John-Keogh/screen-tapper/images/1.0/IMG_0432.jpg

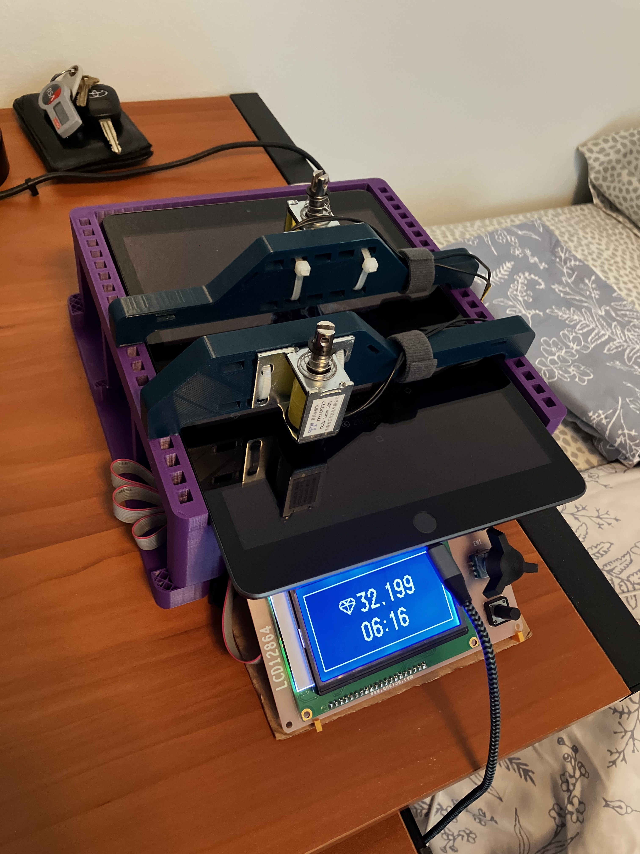
images/1.0/IMG_0432.jpg
