John-Keogh/screen-tapper/images/1.2/IMG_0666.jpg

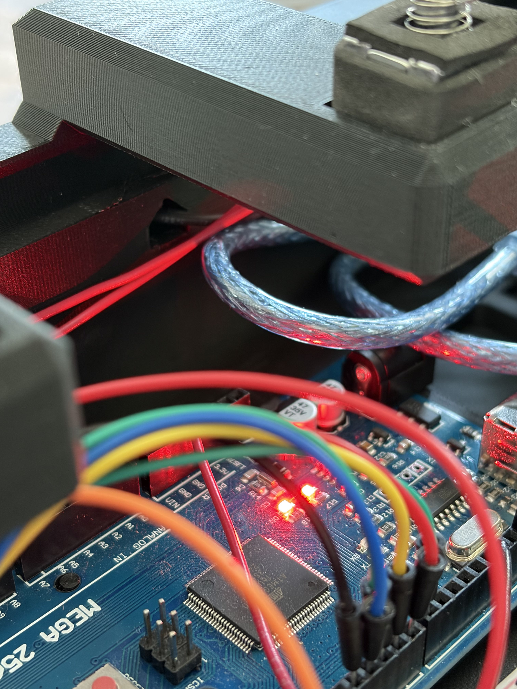
images/1.2/IMG_0666.jpg
