John-Keogh/screen-tapper/hardware/Screen Tapper v1.0.kicad_sch

## KiCad design hardware/Screen Tapper v1.0.kicad_sch (2026-01-04)

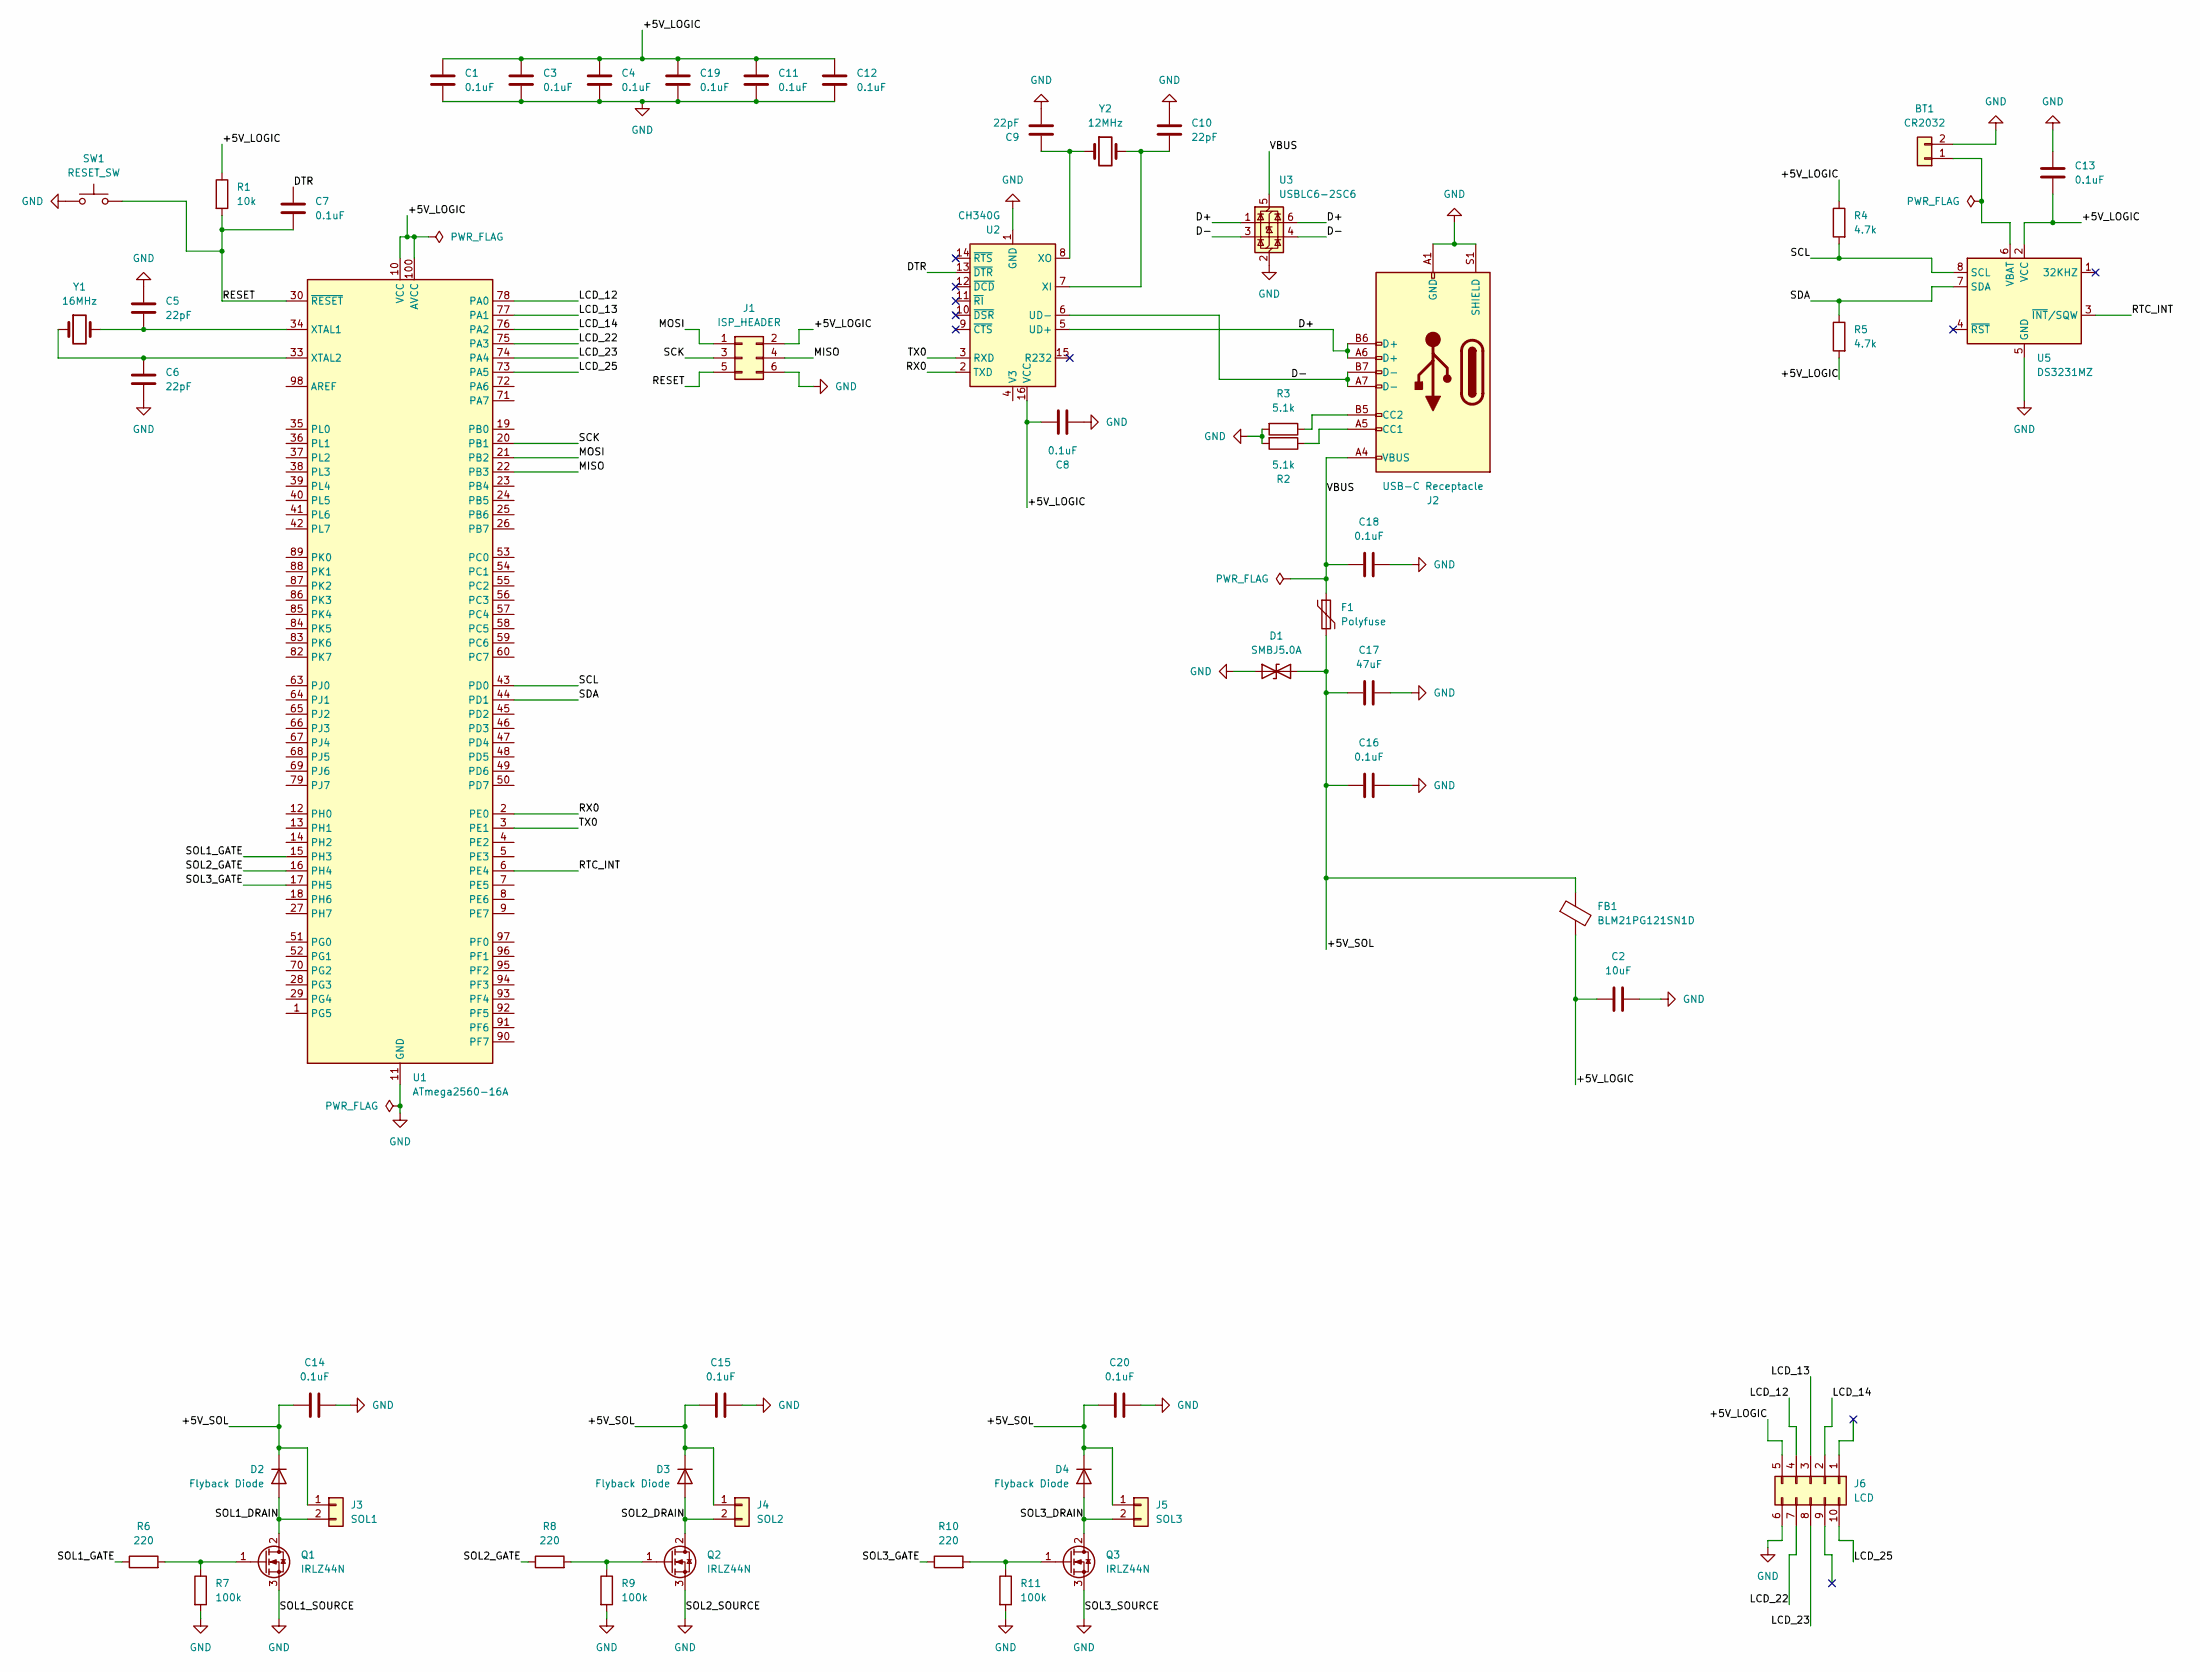
[picture p19: schematic Screen Tapper v1.0.kicad_sch]

Parts:
BT1: CR2032
C1, C3, C4, C7, C8, C11, C12, C13, C14, C15, C16, C18, C19, C20: 0.1uF
C2: 10uF
C5, C6, C9, C10: 22pF
C17: 47uF
D1: SMBJ5.0A
D2, D3, D4: Flyback Diode
F1: Polyfuse
FB1: BLM21PG121SN1D
J1: ISP_HEADER
J2: USB-C Receptacle
J3: SOL1
J4: SOL2
J5: SOL3
J6: LCD
Q1, Q2, Q3: IRLZ44N
R1: 10k
R2, R3: 5.1k
R4, R5: 4.7k
R6, R8, R10: 220
R7, R9, R11: 100k
SW1: RESET_SW
U1: ATmega2560-16A; TQFP-100_14x14mm_P0.5mm
U2: CH340G; SOIC-16_3.9x9.9mm_P1.27mm
U3: USBLC6-2SC6; SOT-23-6
U5: DS3231MZ; SOIC-8_3.9x4.9mm_P1.27mm
Y1: 16MHz
Y2: 12MHz

Connections:
+5V_LOGIC: C1.1, C2.1, C3.1, C4.1, C8.2, C11.1, C12.1, C13.2, C19.1, FB1.2, J1.2, J6.5, R1.1, R4.1, R5.2, U1.10 (VCC), U1.31 (VCC), U1.61 (VCC), U1.80 (VCC), U1.100 (AVCC), U2.16 (VCC), U5.2 (VCC)
+5V_SOL: C14.1, C15.1, C16.1, C17.1, C20.1, D1.2 (A2), D2.1 (K), D3.1 (K), D4.1 (K), F1.2, FB1.1, J3.1, J4.1, J5.1
D+: J2.A6 (D+), J2.B6 (D+), U2.5 (UD+), U3.1 (I/O1), U3.6 (I/O1)
D-: J2.A7 (D-), J2.B7 (D-), U2.6 (UD-), U3.3 (I/O2), U3.4 (I/O2)
DTR: C7.1, U2.13 (~DTR)
GND: BT1.2, C1.2, C2.2, C3.2, C4.2, C5.1, C6.2, C8.1, C9.2, C10.1, C11.2, C12.2, C13.1, C14.2, C15.2, C16.2, C17.2, C18.1, C19.2, C20.2, D1.1 (A1), J1.6, J2.A1 (GND), J2.A12 (GND), J2.B1 (GND), J2.B12 (GND), J2.S1 (SHIELD), J6.6, Q1.3 (S), Q2.3 (S), Q3.3 (S), R2.2, R3.2, R7.2, R9.2, R11.2, SW1.1, U1.11 (GND), U1.32 (GND), U1.62 (GND), U1.81 (GND), U1.99 (GND), U2.1 (GND), U3.2 (GND), U5.5 (GND)
LCD_12: J6.4, U1.78 (PA0)
LCD_13: J6.3, U1.77 (PA1)
LCD_14: J6.2, U1.76 (PA2)
LCD_22: J6.7, U1.75 (PA3)
LCD_23: J6.8, U1.74 (PA4)
LCD_25: J6.10, U1.73 (PA5)
MISO: J1.4, U1.22 (PB3)
MOSI: J1.1, U1.21 (PB2)
unnamed: BT1.1, U5.6 (VBAT)
unnamed: C5.2, U1.34 (XTAL1), Y1.2
unnamed: C6.1, U1.33 (XTAL2), Y1.1
unnamed: C9.1, U2.8 (XO), Y2.1
unnamed: C10.2, U2.7 (XI), Y2.2
unnamed: J2.A5 (CC1), R2.1
unnamed: J2.B5 (CC2), R3.1
unnamed: Q1.1 (G), R6.2, R7.1
unnamed: Q2.1 (G), R8.2, R9.1
unnamed: Q3.1 (G), R10.2, R11.1
RESET: C7.2, J1.5, R1.2, SW1.2, U1.30 (~RESET)
RTC_INT: U1.6 (PE4), U5.3 (~INT/SQW)
RX0: U1.2 (PE0), U2.2 (TXD)
SCK: J1.3, U1.20 (PB1)
SCL: R4.2, U1.43 (PD0), U5.8 (SCL)
SDA: R5.1, U1.44 (PD1), U5.7 (SDA)
SOL1_DRAIN: D2.2 (A), J3.2, Q1.2 (D)
SOL1_GATE: R6.1, U1.15 (PH3)
SOL2_DRAIN: D3.2 (A), J4.2, Q2.2 (D)
SOL2_GATE: R8.1, U1.16 (PH4)
SOL3_DRAIN: D4.2 (A), J5.2, Q3.2 (D)
SOL3_GATE: R10.1, U1.17 (PH5)
TX0: U1.3 (PE1), U2.3 (RXD)
VBUS: C18.2, F1.1, J2.A4 (VBUS), J2.A9 (VBUS), J2.B4 (VBUS), J2.B9 (VBUS), U3.5 (VBUS)
