John-Keogh/screen-tapper/hardware/screen_tapper_pcb.kicad_sch

## KiCad design hardware/screen_tapper_pcb.kicad_sch (2025-07-18)

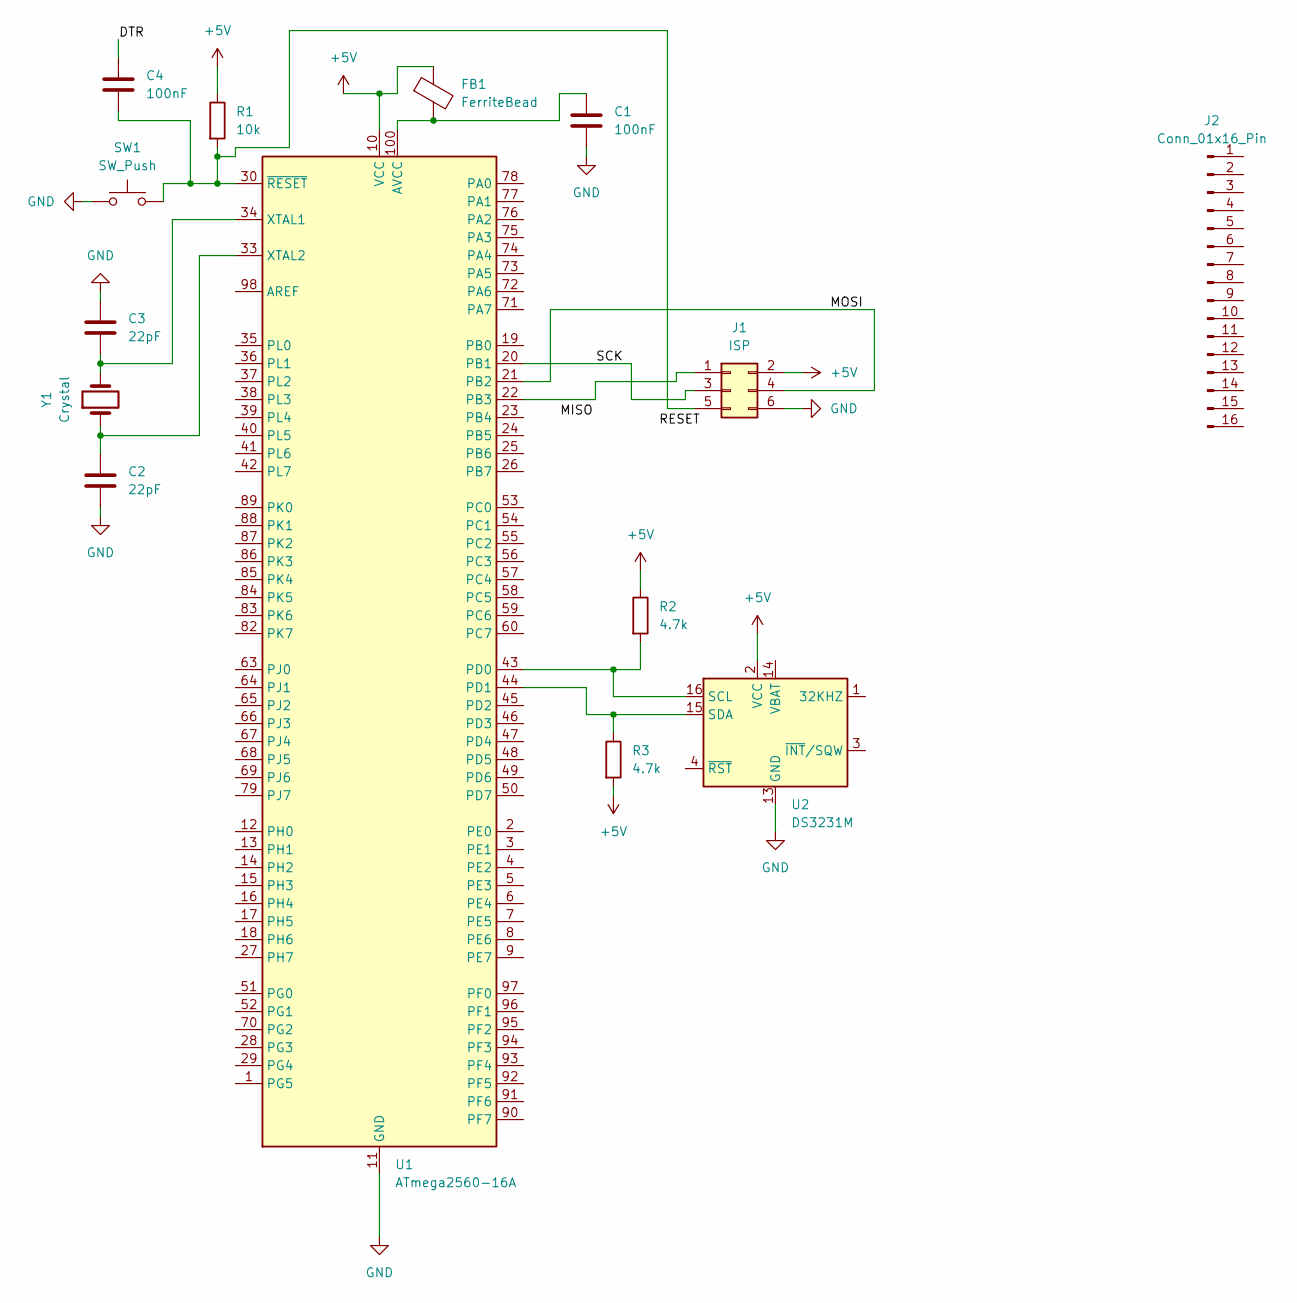
[picture p20: schematic screen_tapper_pcb.kicad_sch]

Parts:
C1, C4: 100nF
C2, C3: 22pF
FB1: FerriteBead
J1: ISP
J2: Conn_01x16_Pin
R1: 10k
R2, R3: 4.7k
SW1: SW_Push
U1: ATmega2560-16A; TQFP-100_14x14mm_P0.5mm
U2: DS3231M; SOIC-16W_7.5x10.3mm_P1.27mm
Y1: Crystal

Connections:
+5V: FB1.1, J1.2, R1.1, R2.1, R3.2, U1.10 (VCC), U1.31 (VCC), U1.61 (VCC), U1.80 (VCC), U2.2 (VCC)
DTR: C4.1
GND: C1.2, C2.2, C3.2, J1.6, SW1.1, U1.11 (GND), U1.32 (GND), U1.62 (GND), U1.81 (GND), U1.99 (GND), U2.5 (GND), U2.6 (GND), U2.7 (GND), U2.8 (GND), U2.9 (GND), U2.10 (GND), U2.11 (GND), U2.12 (GND), U2.13 (GND)
MOSI: J1.4, U1.21 (PB2)
unnamed: C1.1, FB1.2, U1.100 (AVCC)
unnamed: C2.1, U1.33 (XTAL2), Y1.1
unnamed: C3.1, U1.34 (XTAL1), Y1.2
unnamed: C4.2, J1.5, R1.2, SW1.2, U1.30 (~RESET)
unnamed: J1.1, U1.22 (PB3)
unnamed: R2.2, U1.43 (PD0), U2.16 (SCL)
unnamed: R3.1, U1.44 (PD1), U2.15 (SDA)
SCK: J1.3, U1.20 (PB1)
