John-Keogh/screen-tapper/images/1.2/IMG_0661.jpg

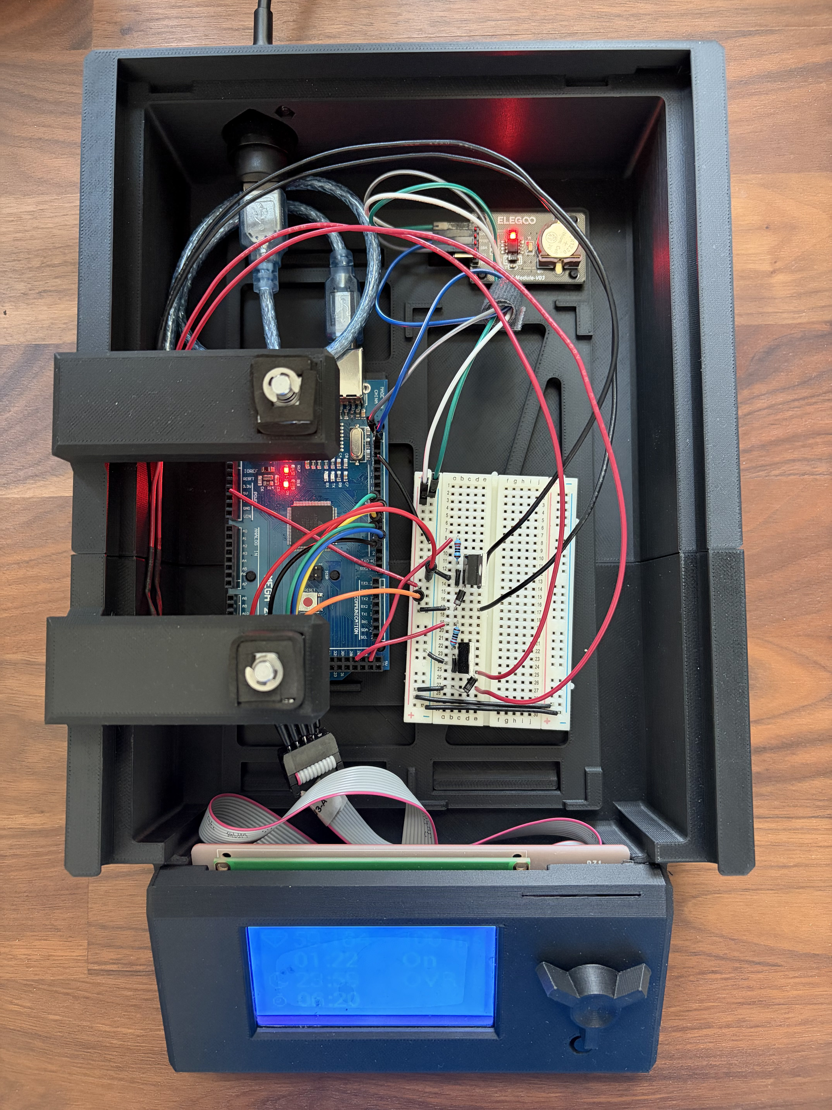
images/1.2/IMG_0661.jpg
