John-Keogh/screen-tapper/images/1.2/IMG_0663.jpg

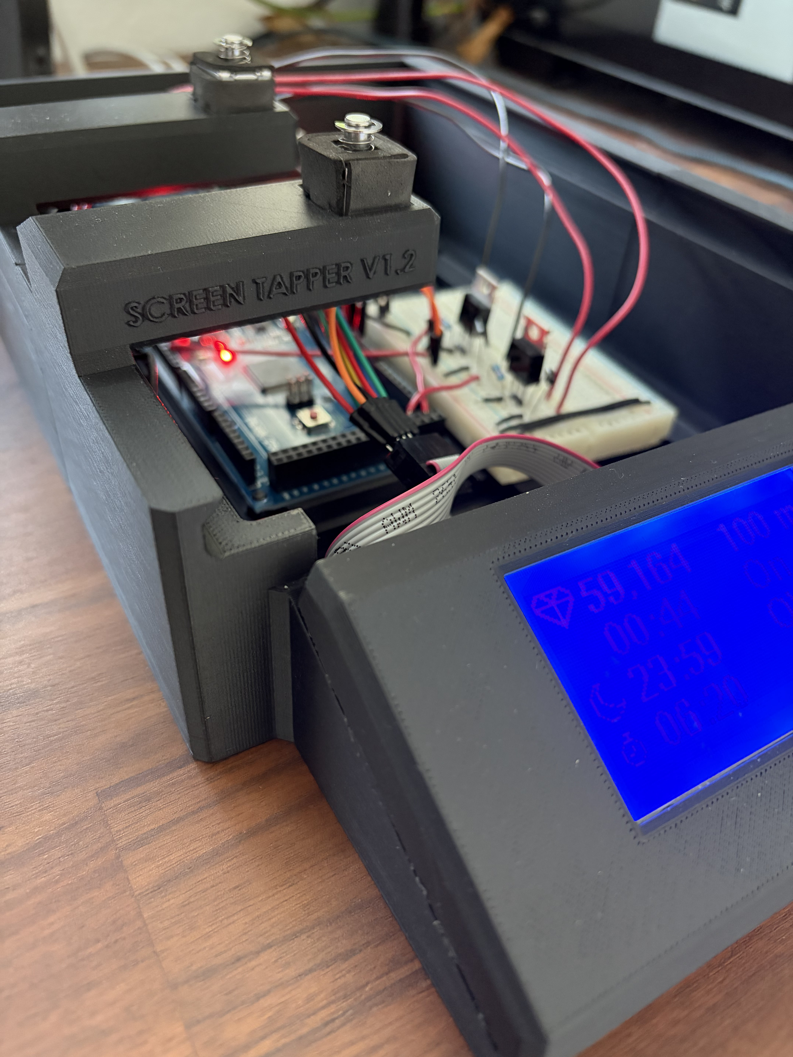
images/1.2/IMG_0663.jpg
