John-Keogh/screen-tapper/images/1.2/IMG_0669.jpg

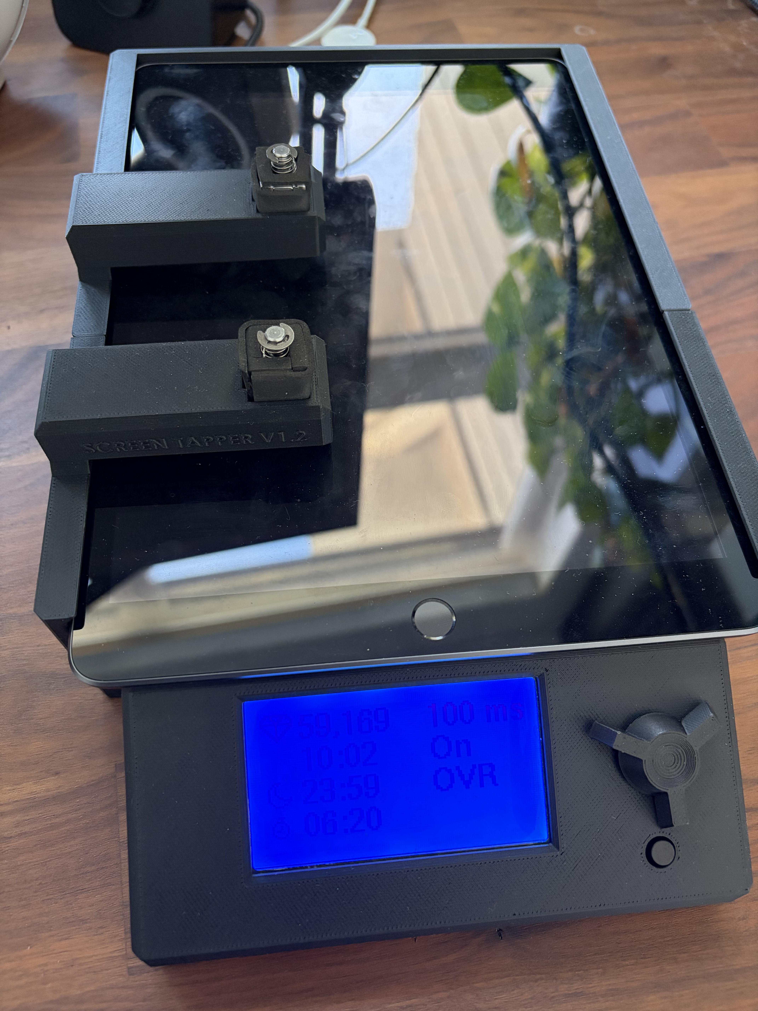
images/1.2/IMG_0669.jpg
