John-Keogh/screen-tapper/images/beta/IMG_9932.jpeg

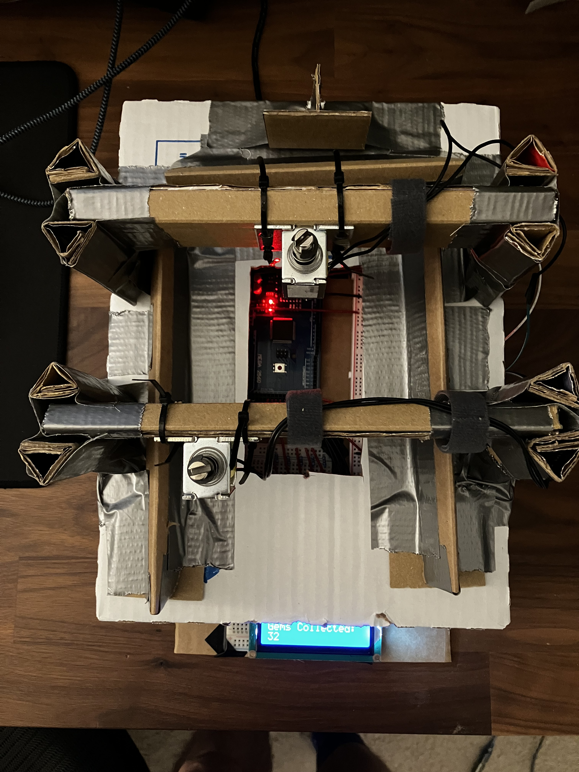
images/beta/IMG_9932.jpeg
