John-Keogh/screen-tapper/images/beta/IMG_9933.jpeg

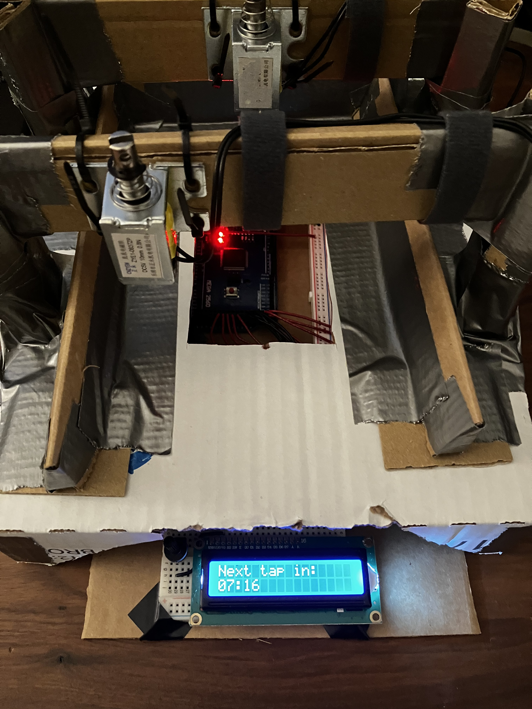
images/beta/IMG_9933.jpeg
